dnewcome/flexisette/assets/cassette-shell-minecraft/836410-minecraft-soundtrack-cassette-shell-remix-2140eeee-dc31-4851-8097-9cc3e82ca437.pdf

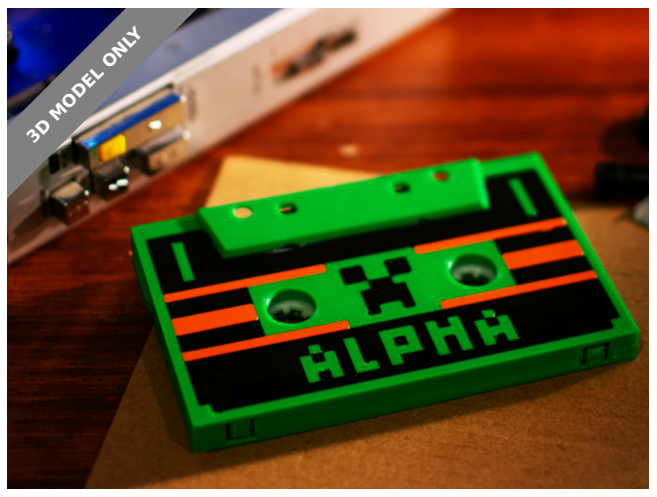
[picture p3: figure]
3D MODEL ONLY

## Summary

Some practical and novelty changes to the cassette shell model by Erik C

Hobby & Makers (https://printables.com/model?categoryId=48) > Music (https://printables.com/model?categoryId=95)

Tags: | cassette | cassettetape

Its a cassette, but you print it. Not much practical use outside perhaps for artists or tape loop creators wanting to experiment with custom shells. The two parts of each half are glued together with superglue, see video for more details.
Original Model: https://www.printables.com/model/176745-cassette-shellsides-a-b (https://www.printables.com/model/176745-cassette-shell-sides-a-b)
Video:

Chris Borge (https://printables.com/@ChrisBorge)

## Minecraft Soundtrack Cassette Shell Remix

VIEW IN BROWSER (https://printables.com/model/836410-minecraft-soundtrack-cassette-shell-remix)

updated 8. 4. 2024 | published 8. 4. 2024

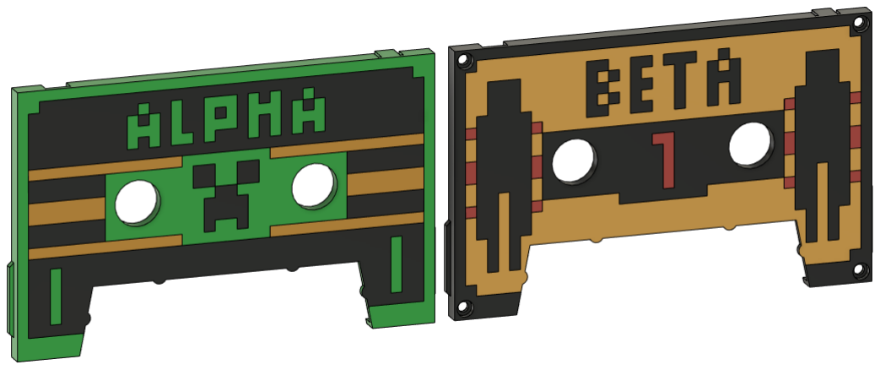
[picture p4: figure]

## Model files

## This remix is based on

Cassette Shell (Sides A & B) (https://printables.com/model/176745-cassette-shell-sides-a-b) by Erik C (https://printables.com/@ErikC_254696)

- Minecraft | 4 files

alpha-side-1.stl

beta-side-2.stl

beta-side-1.stl

## License

This work is licensed under a
Creative Commons (4.0 International License)

Attribution (http://creativecommons.org/licenses/by/4.0/)

✖ | Sharing without ATTRIBUTION
✔ | Remix Culture allowed
✔ | Commercial Use
✔ | Free Cultural Works
✔ | Meets Open Definition

alpha-side-2.stl

side-1-plain.stl

side-2-plain.stl

side-1-insert.stl

side-2-insert.stl

cassettes-remix.step
