dnewcome/flexisette/assets/cassette-shell/176745-cassette-shell-sides-a-b-63550849-6619-4838-8c2e-46b15f5bc81b.pdf

# Cassette Shell

# (Sides A & B)

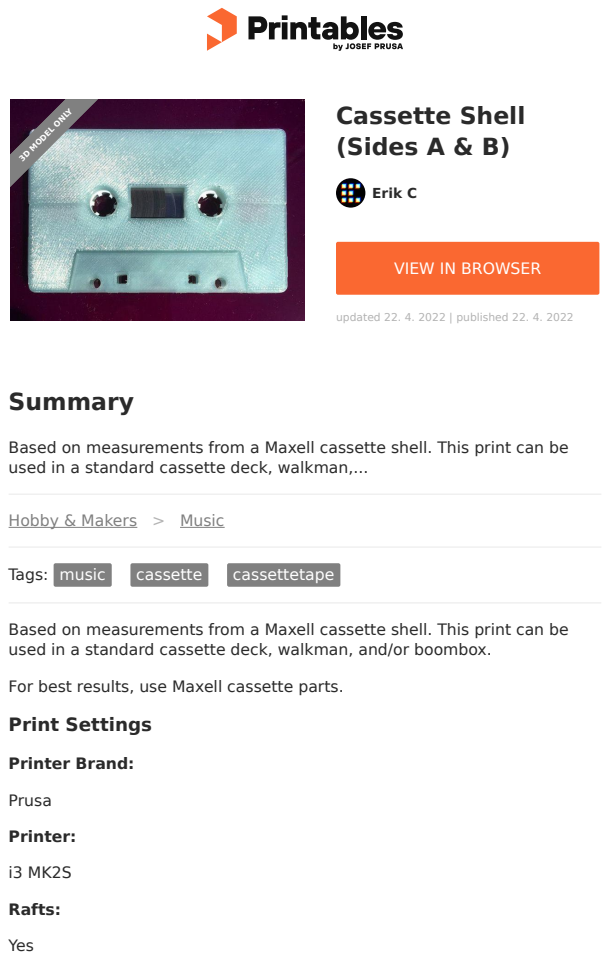
[picture p5: page 1]
Summary; Hobby & Makers; Music; Tags: music; cassette; cassettetape; Print Settings; Printer Brand:; Prusa; Printer:; Rafts:; Yes; Erik C; updated 22. 4. 2022 | published 22. 4. 2022; 3D MODEL ONLY

VIEW IN BROWSER (https://www.printables.com/model/176745-cassette-shell-sides-a-b)

Based on measurements from a Maxell cassette shell. This print can be
used in a standard cassette deck, walkman,...

used in a standard cassette deck, walkman, and/or boombox.

For best results, use Maxell cassette parts.

# Model files

### Supports:

Yes

Category: Music

Find source .stl files on Thingiverse.com (https://www.thingiverse.com/thing:2933735)

# License

This work is licensed under a

Creative Commons (4.0 International License)

Attribution (http://creativecommons.org/licenses/by/4.0/)

✖ | Sharing without ATTRIBUTION
✔ | Remix Culture allowed
✔ | Commercial Use
✔ | Free Cultural Works
✔ | Meets Open Definition

cassette_tape_-_side_2.step

cassette_tape_-_side_b.stl

cassette_tape_-_side_1.step

cassette_tape_-_side_a.stl
